HASwitchPlate/HASPone/images/HASP PCB Back.png

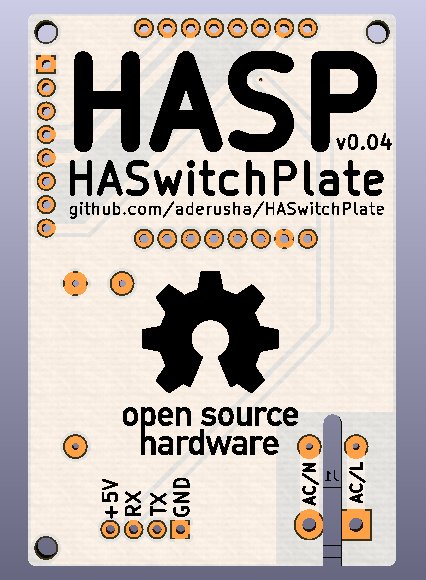
images/HASP PCB Back.png
