HASwitchPlate/HASPone/images/HASP PCB Front.png

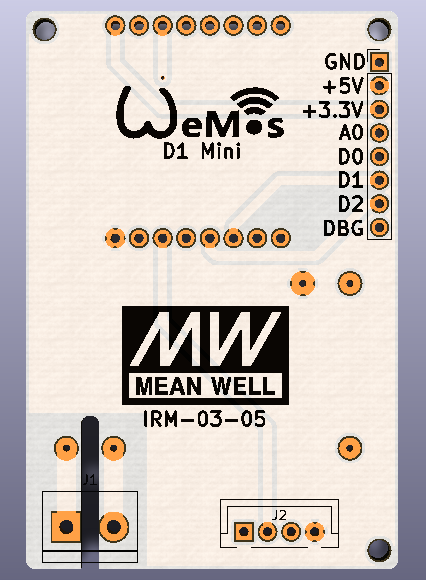
images/HASP PCB Front.png
