HASwitchPlate/HASPone/images/HASPone_core_functionality_blueprint_YouTube.png

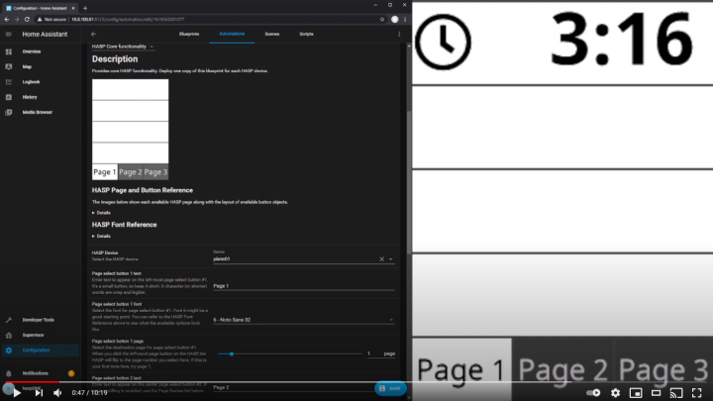
images/HASPone_core_functionality_blueprint_YouTube.png
