HASwitchPlate/HASPone/images/HASwitchPlate_Demo_3x3.png

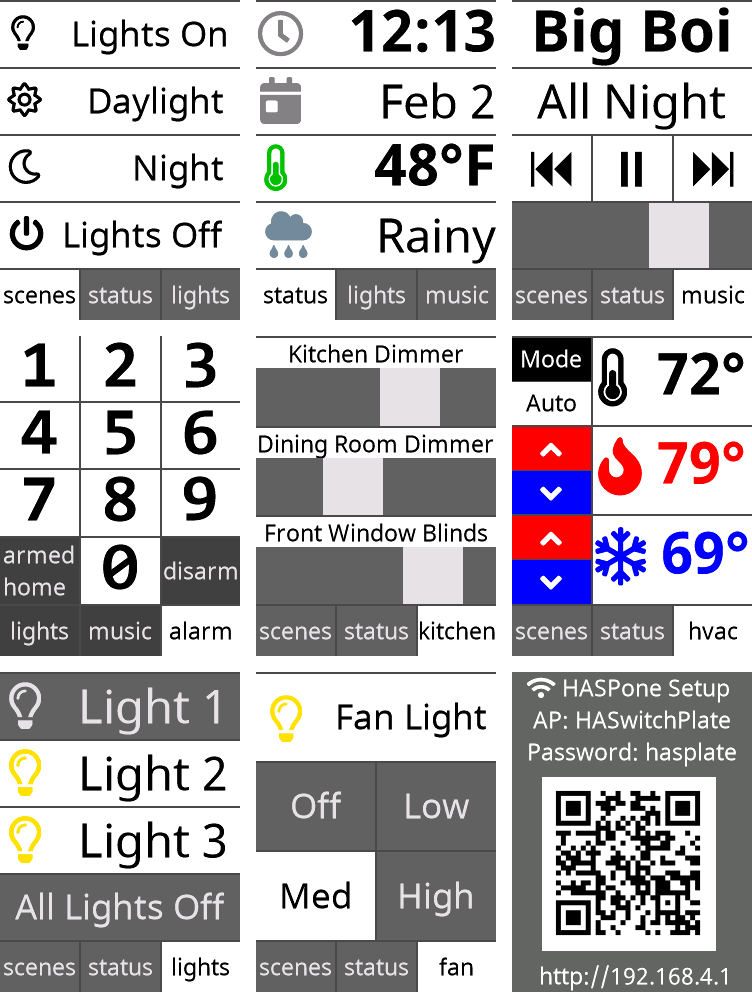
images/HASwitchPlate_Demo_3x3.png
