HASwitchPlate/HASPone/images/NextionUI_p0_Init_Screen.png

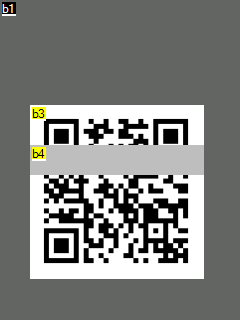
images/NextionUI_p0_Init_Screen.png
