HASwitchPlate/HASPone/images/NextionUI_p9_9buttons.png

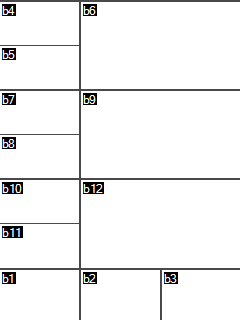
images/NextionUI_p9_9buttons.png
