HASwitchPlate/HASPone/images/NextionUI_p10_5buttons.png

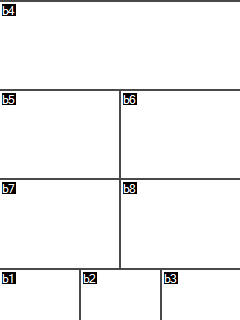
images/NextionUI_p10_5buttons.png
