HASwitchPlate/HASPone/images/NextionUI_p11_1button+1slider.png

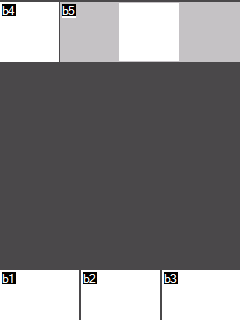
images/NextionUI_p11_1button+1slider.png
