HASwitchPlate/HASPone/images/WiFi_Config_1.png

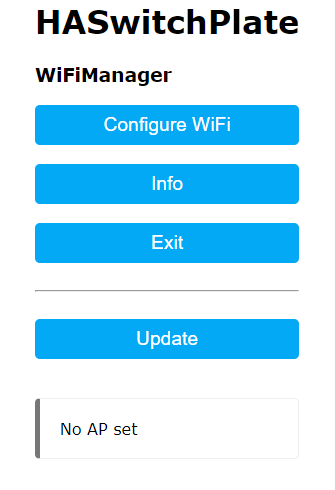
images/WiFi_Config_1.png
