HASwitchPlate/HASPone/images/WiFi_Config_2.png

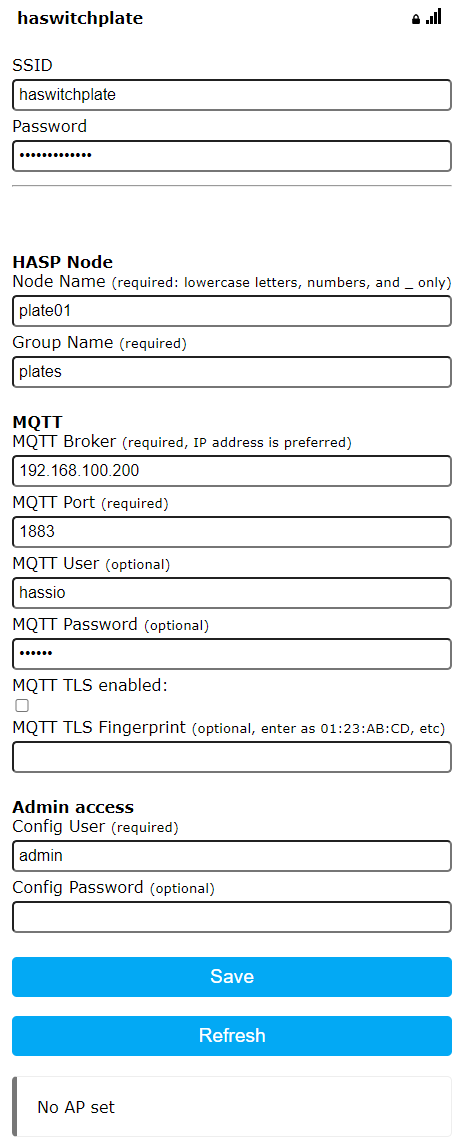
images/WiFi_Config_2.png
