HASwitchPlate/HASPone/3D_Printable_Models/HASwitchPlate_front_5x_decora_decora_hasp_decora_decora.stl

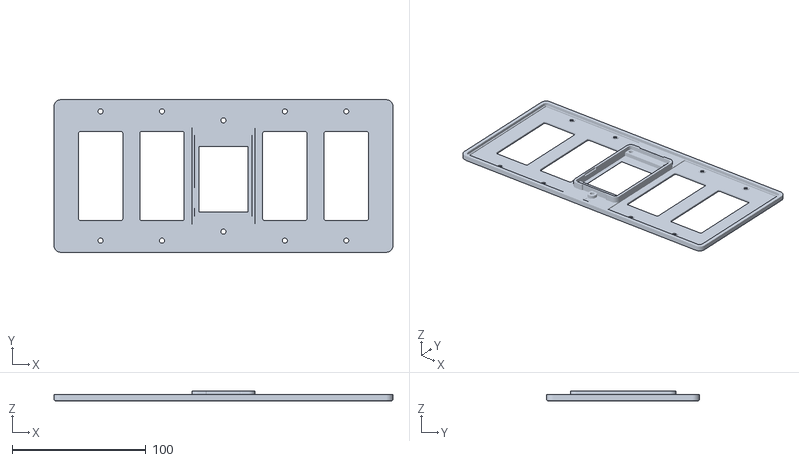
[picture p42: CAD file, 2021-03-01]
3D_Printable_Models/HASwitchPlate_front_5x_decora_decora_hasp_decora_decora.stl
253.9 x 114.3 x 7.70
