HASwitchPlate/HASPone/3D_Printable_Models/HASwitchPlate_rear_lcdmod_minimum_clearance.stl

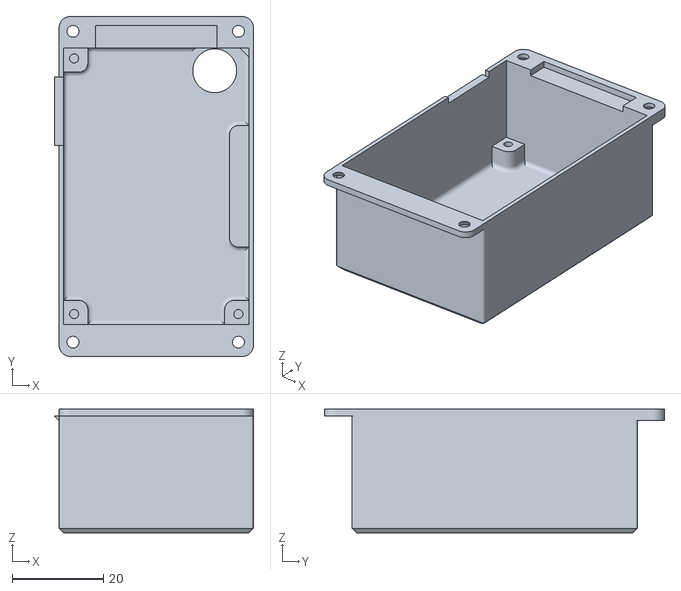
[picture p43: CAD file, 2021-03-01]
3D_Printable_Models/HASwitchPlate_rear_lcdmod_minimum_clearance.stl
43.6 x 74.5 x 27.1
