HASwitchPlate/HASPone/3D_Printable_Models/HASwitchPlate_rear_lcdmod.stl

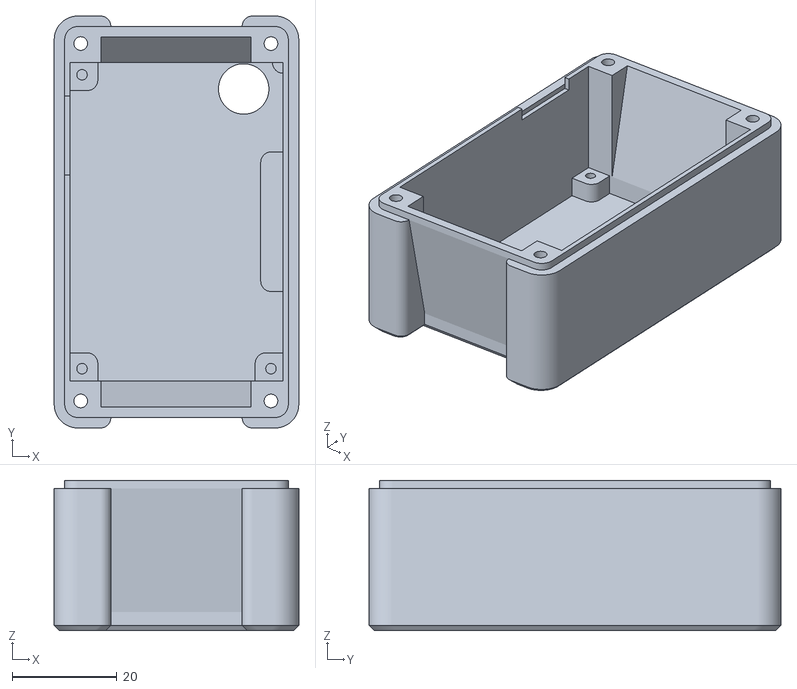
[picture p44: CAD file, 2021-03-01]
3D_Printable_Models/HASwitchPlate_rear_lcdmod.stl
46.6 x 78.5 x 28.6
