HASwitchPlate/HASPone/3D_Printable_Models/HASwitchPlate_rear_dev.stl

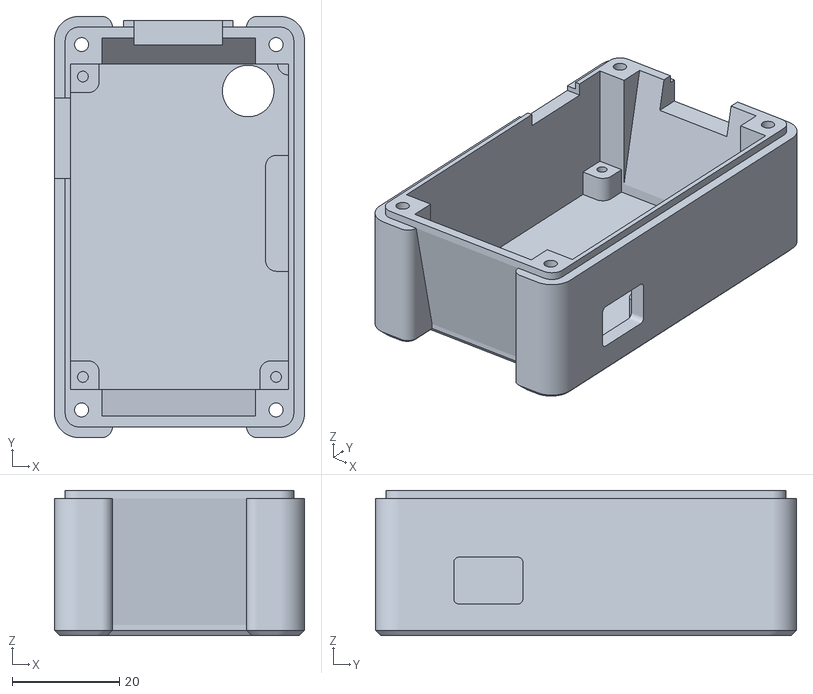
[picture p45: CAD file, 2021-03-01]
3D_Printable_Models/HASwitchPlate_rear_dev.stl
46.6 x 78.5 x 27.1
