HASwitchPlate/HASPone/3D_Printable_Models/HASwitchPlate_front_single_dev.stl

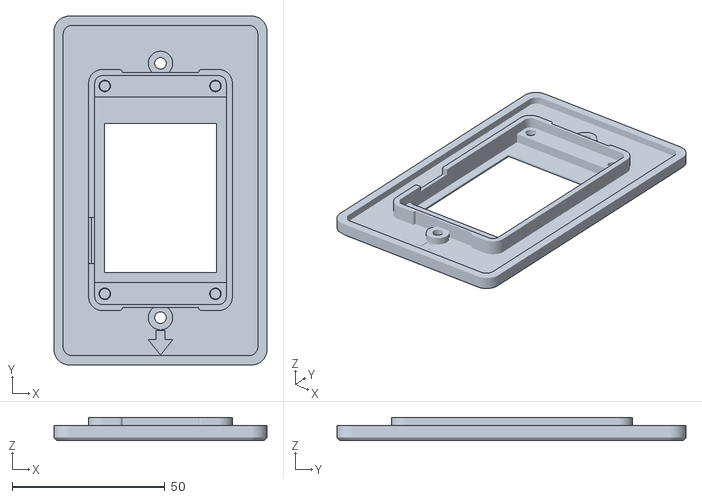
[picture p46: CAD file, 2021-03-01]
3D_Printable_Models/HASwitchPlate_front_single_dev.stl
69.8 x 114.3 x 7.70
