HASwitchPlate/HASPone/3D_Printable_Models/HASwitchPlate_front_single_UK-UNTESTED.stl

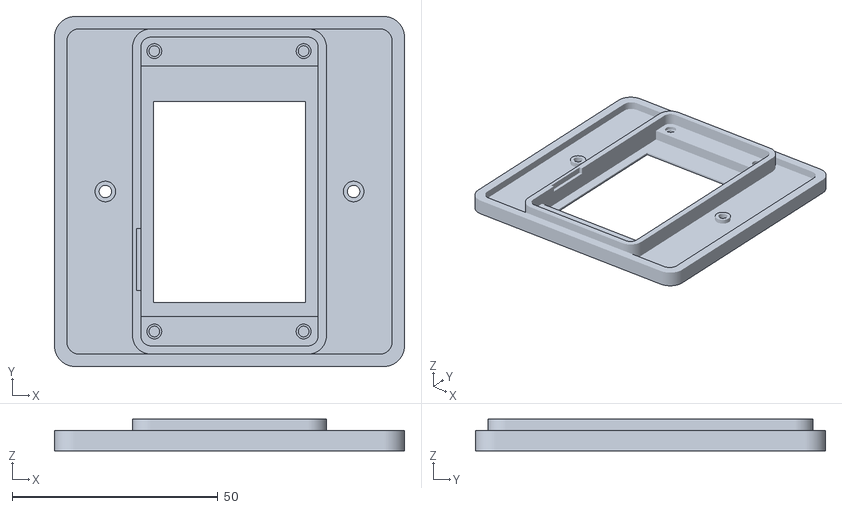
[picture p47: CAD file, 2021-03-01]
3D_Printable_Models/HASwitchPlate_front_single_UK-UNTESTED.stl
85.0 x 85.0 x 7.70
