HASwitchPlate/HASPone/3D_Printable_Models/HASwitchPlate_front_single.stl

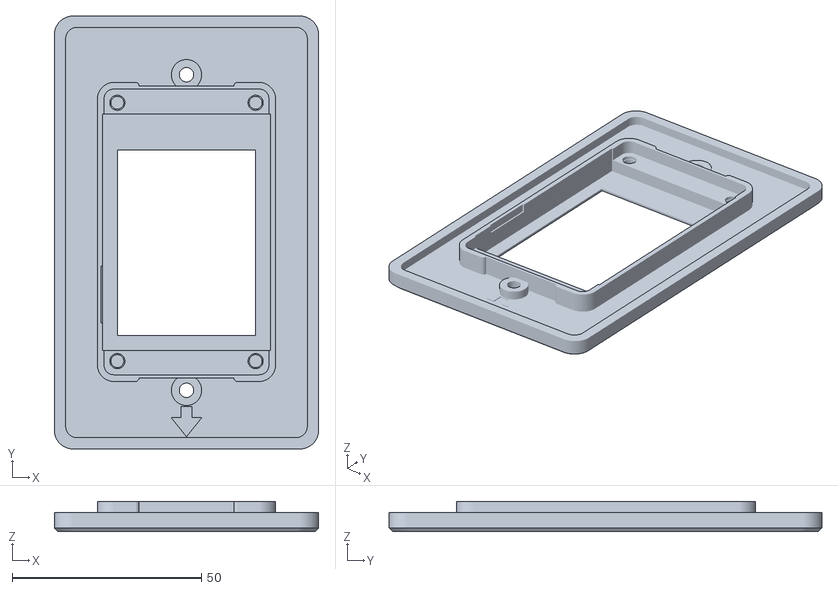
[picture p48: CAD file, 2021-03-01]
3D_Printable_Models/HASwitchPlate_front_single.stl
69.8 x 114.3 x 8.00
