HASwitchPlate/HASPone/3D_Printable_Models/HASwitchPlate_desktop_base.stl

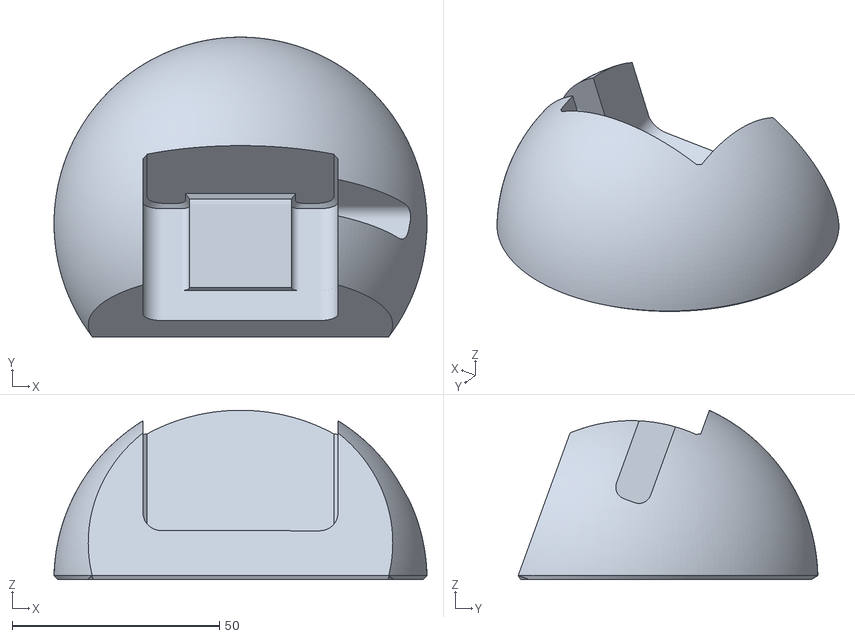
[picture p49: CAD file, 2021-03-01]
3D_Printable_Models/HASwitchPlate_desktop_base.stl
90.0 x 72.3 x 40.9
